MrBlinky/mdmc/pcb/eagle/MDMCv2-board.png

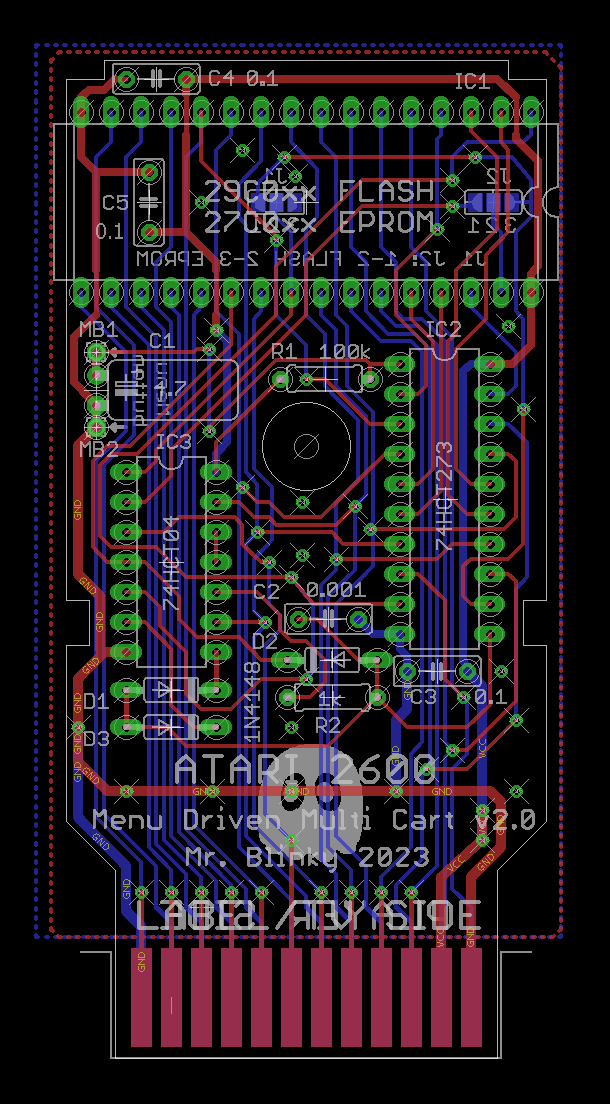
pcb/eagle/MDMCv2-board.png
