MrBlinky/mdmc/pcb/images/pcb-oshpark-render-bottom.png

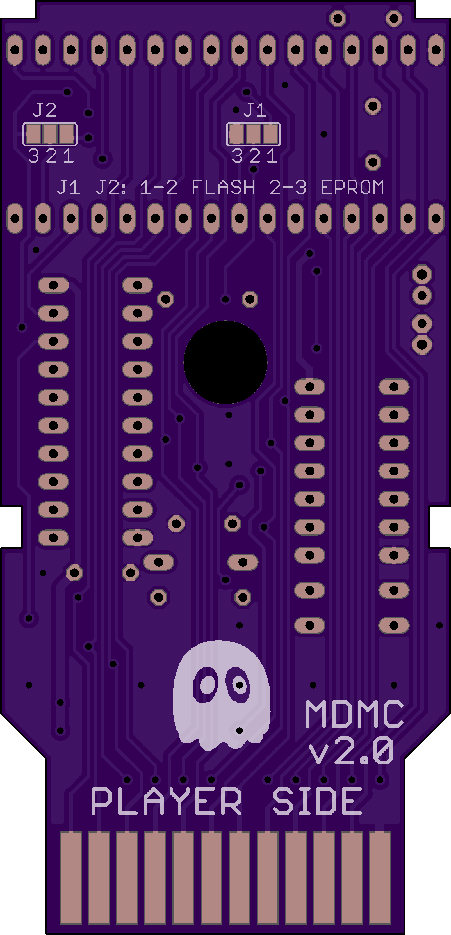
pcb/images/pcb-oshpark-render-bottom.png
