MrBlinky/mdmc/pcb/images/pcb-assembled-bottom.jpg

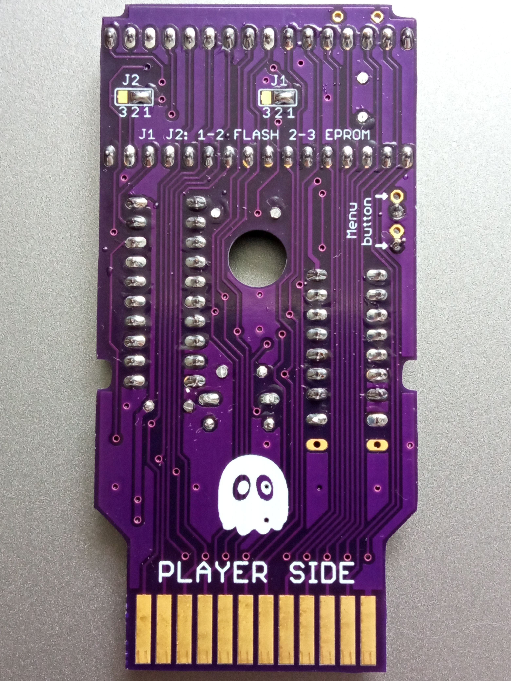
pcb/images/pcb-assembled-bottom.jpg
