MrBlinky/mdmc/pcb/images/pcb-assembled-top.jpg

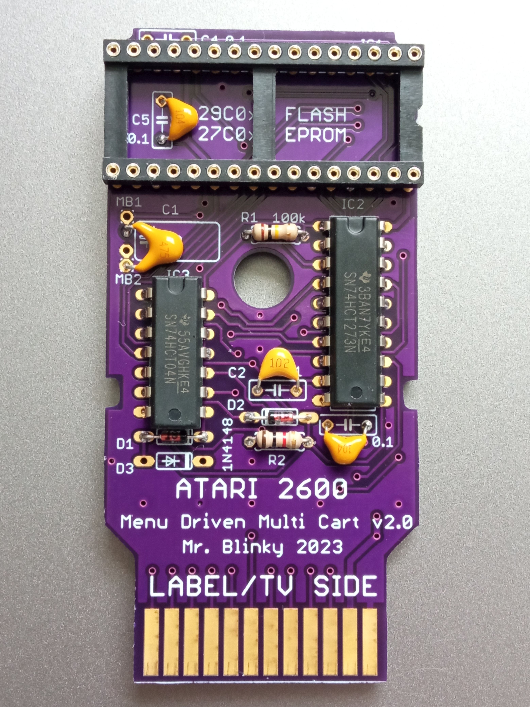
pcb/images/pcb-assembled-top.jpg
